zackattack2130/Phanny/Images/Left Side F Left.jpg

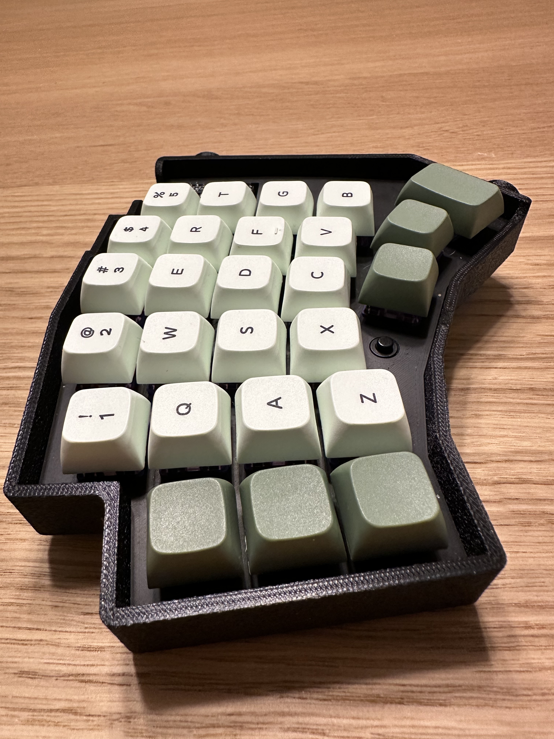
Images/Left Side F Left.jpg
