zackattack2130/Phanny/Images/On Desk.jpg

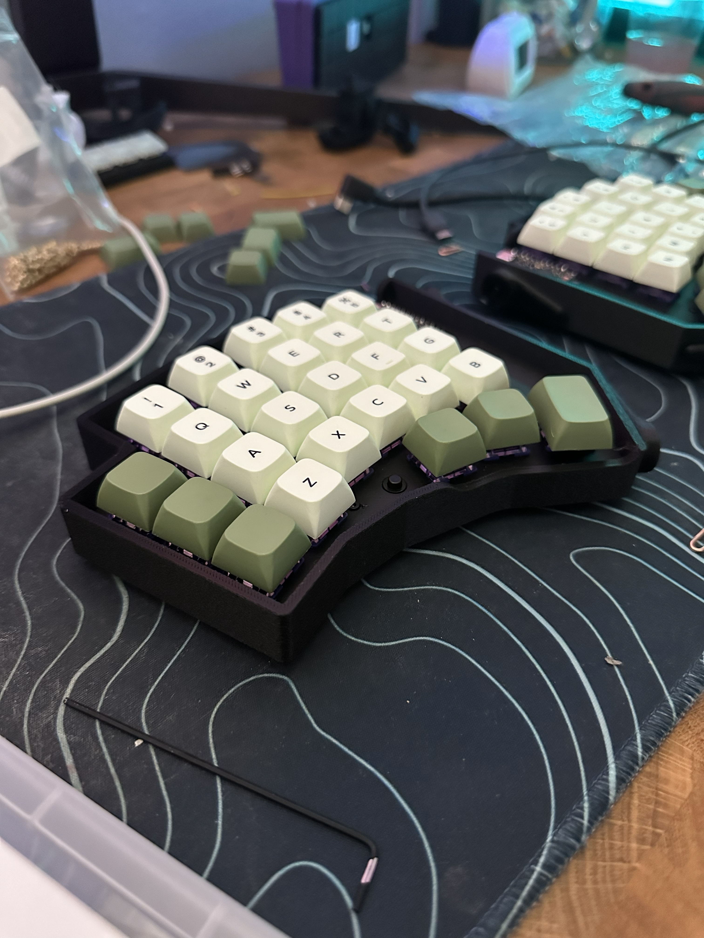
Images/On Desk.jpg
