zackattack2130/Phanny/Images/PCB 3D Viewer Front.jpg

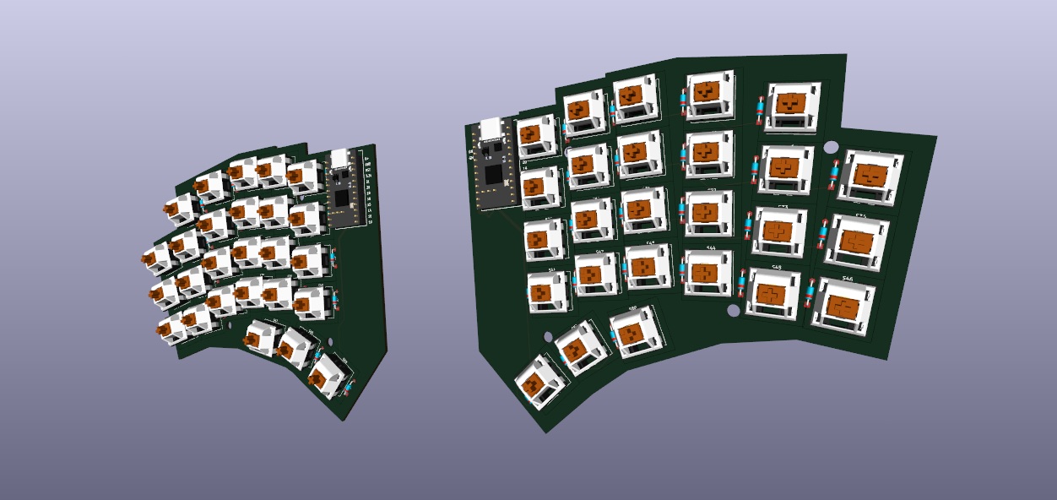
Images/PCB 3D Viewer Front.jpg
