zackattack2130/Phanny/Images/PCB 3D Viewer Rear.jpg

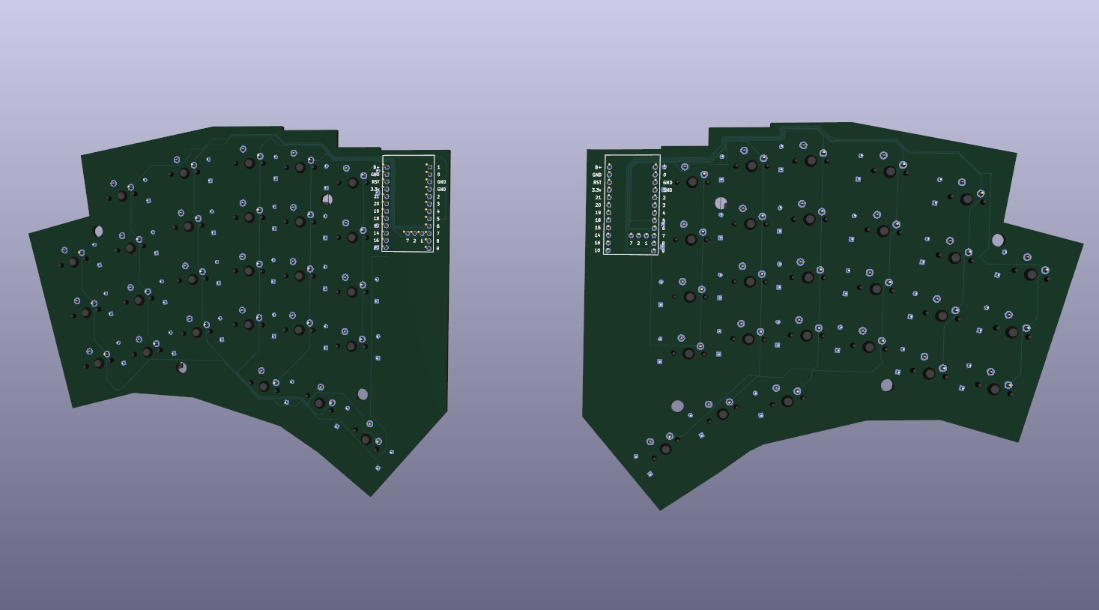
Images/PCB 3D Viewer Rear.jpg
