zackattack2130/Phanny/Images/Bottom Case.jpg

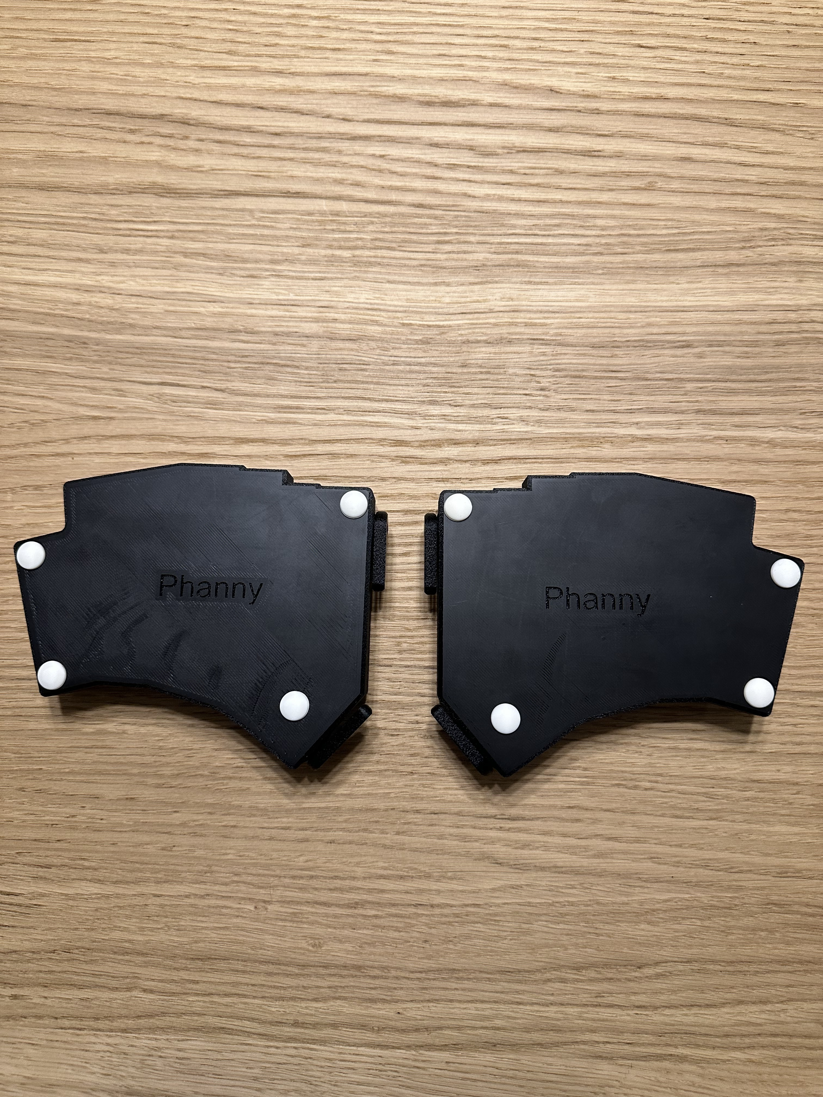
Images/Bottom Case.jpg
